AP-IT-GH/iot19-md2/src/Angular/medicaldelivery/src/assets/box.png

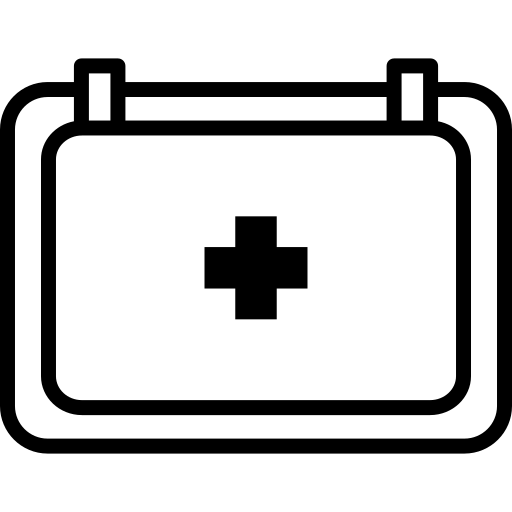
src/Angular/medicaldelivery/src/assets/box.png
