AP-IT-GH/iot19-md2/src/pcb/img/humidity_sensor.png

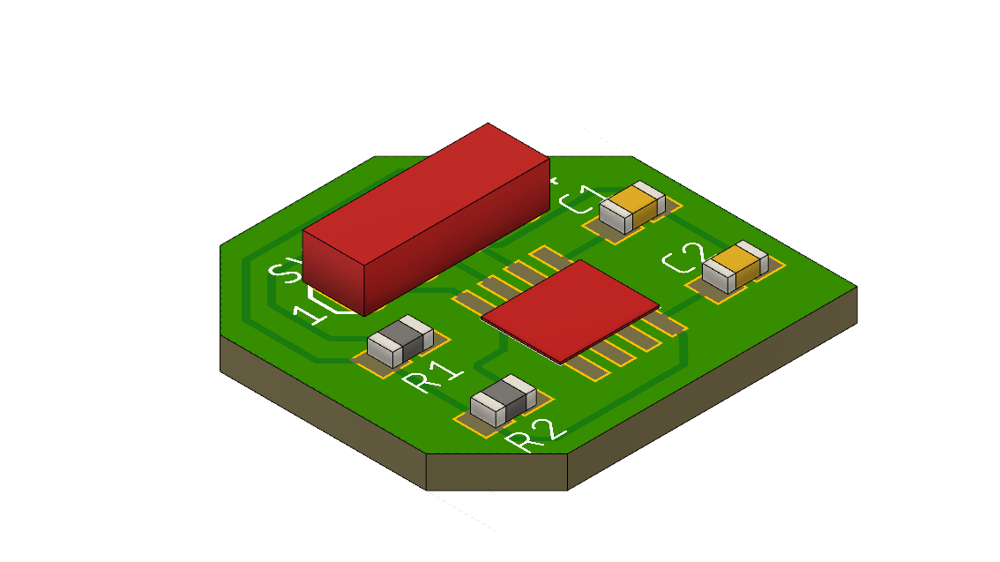
src/pcb/img/humidity_sensor.png
