AP-IT-GH/iot19-md2/src/9DOF/9dofTesting/9dofTesting.ino

//9Dof

#include <SPI.h> // SPI library included for SparkFunLSM9DS1
#include <Wire.h> // I2C library included for SparkFunLSM9DS1
#include <SparkFunLSM9DS1.h> // SparkFun LSM9DS1 library


LSM9DS1 imu;
#define LSM9DS1_M  0x1E // Would be 0x1C if SDO_M is LOW
#define LSM9DS1_AG  0x6B // Would be 0x6A if SDO_AG is LOW


float rotation = 0;
float tau=0.075;
float a=0.0;

#define PRINT_CALCULATED
//#define PRINT_RAW
#define PRINT_SPEED 250 // 250 ms between prints

static unsigned long lastPrint = 0; // Keep track of print time


void init9Dof() {
  
  imu.settings.device.commInterface = IMU_MODE_I2C;
  imu.settings.device.mAddress = LSM9DS1_M;
  imu.settings.device.agAddress = LSM9DS1_AG;
  imu.begin();
  
  if (!imu.begin()){
    
      Serial.println("Failed to communicate with LSM9DS1");
      Serial.println("Check connections, and try again.");
      Serial.println();
     while (1);
  }  
  
}
void setup() {
Serial.begin(115200);
Serial.print("Serial Started");
init9Dof();

}

void loop() {
//ReadGforce();
ReadRotation();
NotFacingTop(rotation,102.0);
}
void ReadGforce()
{
 
  // To read from the accelerometer, you must first call the
  // readAccel() function. When this exits, it'll update the
  // ax, ay, and az variables with the most current data.
   if ( imu.accelAvailable() ){
  imu.readAccel();
   }
  float accelX = imu.calcAccel(imu.ax);
  float accelY = imu.calcAccel(imu.ay);
  float accelZ = imu.calcAccel(imu.az);
  
 // total acceleration
  float acceltot = sqrt(pow(accelX,2)+pow(accelY,2)+pow(accelZ,2));
 
  float accfilterdX = accelX/acceltot;
  float accfilterdY = accelY/acceltot;
  float accfilterdZ = accelY/acceltot; 

    if ((lastPrint + PRINT_SPEED) < millis())
  {
    
  Serial.print("X: ");
  Serial.print(accfilterdX);
  Serial.print("Y: ");
  Serial.print(", ");
  Serial.print(accfilterdY);
   Serial.print("Z: ");
  Serial.print(", ");
  Serial.println(accfilterdZ);
  Serial.println();

  
  }

  delay (500);
}
void ReadRotation() {
  



  // Update the sensor values whenever new data is available
  if ( imu.gyroAvailable() )
  {
    // update gx, gy, and gz variables with the most current data.
    imu.readGyro();
  }
   if ( imu.accelAvailable() ){
  imu.readAccel();
   }
  float accelX = imu.calcAccel(imu.ax);
  float accelY = imu.calcAccel(imu.ay);
  float accelZ = imu.calcAccel(imu.az);

   
   //to do add Y AND X BASE TO control value
   //Accelerometer for better values
  float roll = atan2(accelY , accelZ) * 57.3; 


  // Serial.print("roll :  ");
 //  Serial.println(roll);

  //complementaire filter
  float f_gz = imu.calcGyro(imu.gz);
  float dtC = float(millis())/1000.0;
  a=tau/(tau+dtC);
  rotation = a* (rotation + f_gz * dtC) + (1-a) * (roll);
       Serial.print("rotation :  ");
       Serial.println(abs(rotation));
   }

bool NotFacingTop(float degreesRotation, float degreesFactingTop){
  //Filter 
  
  if ((abs(degreesRotation) >= degreesFactingTop)) return true;
  else return false;
  }  
